filipamator/vu_meter/fake_dac.vhd

library IEEE;
use IEEE.STD_LOGIC_1164.ALL;
use ieee.numeric_std.all;


entity fake_dac is
port (
        clock       : in STD_LOGIC;
        reset       : in STD_LOGIC;
        data_out    : out STD_LOGIC_VECTOR(15 downto 0);
        data_out_en : out STD_LOGIC
);
end fake_dac;


architecture Behavioral of fake_dac is


component gen48khz is
generic (
		CLKCOUNTER	: natural := 1000
);
port (
		clock 	: in std_logic;
		reset_n	: in std_logic;
		enable	: out std_logic
);
end component gen48khz;


signal counter      : integer;
signal sample_addr : integer range 0 to 8191;
signal sample_value  : STD_LOGIC_VECTOR(15 downto 0);

signal tick,reset_n : STD_LOGIC;

begin

reset_n <= not reset;

gen48khz_i1 : gen48khz
generic map (
		CLKCOUNTER  => 1000 -- 1000
)
port map (
		clock       => clock,
		reset_n     => reset_n,
		enable      => tick
);


process (clock,reset) 
begin
    if reset='1' then
        sample_addr <= 0;
    elsif clock='1' and clock'event then
        if tick='1' then
            data_out <= sample_value;
            data_out_en <= '1';
            if sample_addr=8191 then
                sample_addr <= 0;
            else
                sample_addr <= sample_addr + 1;
            end if;
        else
            data_out_en <= '0';
        end if;
    end if;
end process;


with sample_addr select sample_value <=
"0000000000000000" when 0,
"0011001011000110" when 1,
"0011110111010001" when 2,
"0001100001111101" when 3,
"1110000000000001" when 4,
"1100000010001101" when 5,
"1101001010111111" when 6,
"0000100001011010" when 7,
"0011011101101100" when 8,
"0011101100100000" when 9,
"0001000010010000" when 10,
"1101100100001011" when 11,
"1100000000000001" when 12,
"1101100100001011" when 13,
"0001000010010000" when 14,
"0011101100100000" when 15,
"0011011101101100" when 16,
"0000100001011010" when 17,
"1101001010111111" when 18,
"1100000010001101" when 19,
"1110000000000000" when 20,
"0001100001111101" when 21,
"0011110111010001" when 22,
"0011001011000110" when 23,
"0000000000000000" when 24,
"1100110100111010" when 25,
"1100001000101111" when 26,
"1110011110000011" when 27,
"0001111111111111" when 28,
"0011111101110011" when 29,
"0010110101000001" when 30,
"1111011110100110" when 31,
"1100100010010100" when 32,
"1100010011100000" when 33,
"1110111101110000" when 34,
"0010011011110101" when 35,
"0011111111111111" when 36,
"0010011011110110" when 37,
"1110111101110000" when 38,
"1100010011100000" when 39,
"1100100010010011" when 40,
"1111011110100110" when 41,
"0010110101000001" when 42,
"0011111101110011" when 43,
"0010000000000000" when 44,
"1110011110000011" when 45,
"1100001000101111" when 46,
"1100110100111010" when 47,
"0000000000000000" when 48,
"0011001011000110" when 49,
"0011110111010001" when 50,
"0001100001111110" when 51,
"1110000000000001" when 52,
"1100000010001101" when 53,
"1101001010111111" when 54,
"0000100001011010" when 55,
"0011011101101100" when 56,
"0011101100100000" when 57,
"0001000010010000" when 58,
"1101100100001011" when 59,
"1100000000000001" when 60,
"1101100100001010" when 61,
"0001000010010000" when 62,
"0011101100100000" when 63,
"0011011101101101" when 64,
"0000100001011010" when 65,
"1101001010111111" when 66,
"1100000010001101" when 67,
"1110000000000000" when 68,
"0001100001111101" when 69,
"0011110111010001" when 70,
"0011001011000110" when 71,
"0000000000000000" when 72,
"1100110100111010" when 73,
"1100001000101111" when 74,
"1110011110000010" when 75,
"0001111111111111" when 76,
"0011111101110011" when 77,
"0010110101000001" when 78,
"1111011110100110" when 79,
"1100100010010100" when 80,
"1100010011100000" when 81,
"1110111101110000" when 82,
"0010011011110101" when 83,
"0011111111111111" when 84,
"0010011011110110" when 85,
"1110111101110000" when 86,
"1100010011100000" when 87,
"1100100010010011" when 88,
"1111011110100110" when 89,
"0010110101000001" when 90,
"0011111101110011" when 91,
"0010000000000000" when 92,
"1110011110000011" when 93,
"1100001000101111" when 94,
"1100110100111010" when 95,
"0000000000000000" when 96,
"0011001011000110" when 97,
"0011110111010001" when 98,
"0001100001111110" when 99,
"1110000000000001" when 100,
"1100000010001101" when 101,
"1101001010111111" when 102,
"0000100001011010" when 103,
"0011011101101100" when 104,
"0011101100100000" when 105,
"0001000010010000" when 106,
"1101100100001011" when 107,
"1100000000000001" when 108,
"1101100100001010" when 109,
"0001000010010000" when 110,
"0011101100100000" when 111,
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
"0010110100111000" when 3978,
"0011111101110101" when 3979,
"0010000000001010" when 3980,
"1110011110001110" when 3981,
"1100001000110010" when 3982,
"1100110100110011" when 3983,
"1111111111110100" when 3984,
"0011001010111110" when 3985,
"0011110111010100" when 3986,
"0001100010001001" when 3987,
"1110000000001011" when 3988,
"1100000010001110" when 3989,
"1101001010110110" when 3990,
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
