filipamator/vu_meter/hannwindow.vhd

library IEEE;
use IEEE.STD_LOGIC_1164.ALL;
use ieee.numeric_std.all;

entity hannwindow is
port (
        i_sample    : in STD_LOGIC_VECTOR(9 downto 0);
        o_value     : out STD_LOGIC_VECTOR(31 downto 0)
);
end hannwindow;



architecture Behavioral of hannwindow is

signal r_sample : integer range 0 to 1023 := 0;


begin


r_sample <= to_integer(unsigned(i_sample));

with r_sample select o_value  <=
    "00000000000000000000000000000000" when 0,      -- 0.0
    "00110111000111100011100011011000" when 1,      -- 9.430769E-6
    "00111000000111100011100001110111" when 2,      -- 3.7722722E-5
    "00111000101100011111111011001110" when 3,      -- 8.487479E-5
    "00111001000111100011011011101111" when 4,      -- 1.5088519E-4
    "00111001011101110011010000001100" when 5,
    "00111001101100011111101011110000" when 6,
    "00111001111100100011110110101111" when 7,
    "00111010000111100011000011010011" when 8,
    "00111010010010000011001100001110" when 9,
    "00111010011101110010010100100000" when 10,
    "00111010100101011000001101001011" when 11,
    "00111010101100011110101101111000" when 12,
    "00111010110100001100101011010001" when 13,
    "00111010111100100010000100001000" when 14,
    "00111011000010101111011011100110" when 15,
    "00111011000111100001100001100011" when 16,
    "00111011001100100111010011001010" when 17,
    "00111011010010000000101111101010" when 18,
    "00111011010111101101110110001101" when 19,
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
    "00111000101100011111111011001110" when 1020,
    "00111000000111100011100001110111" when 1021,
    "00110111000111100011100011011000" when 1022,
    "00000000000000000000000000000000" when 1023,       -- 0.0
    "00000000000000000000000000000000" when others;

end Behavioral;
