filipamator/vu_meter/fifo_inst.vhd

fifo_inst : fifo PORT MAP (
		clock	 => clock_sig,
		data	 => data_sig,
		rdreq	 => rdreq_sig,
		wrreq	 => wrreq_sig,
		empty	 => empty_sig,
		full	 => full_sig,
		q	 => q_sig,
		usedw	 => usedw_sig
	);
